sankerspace/Blumentopf/SensorNode/SensorNode.ino

/*
   Project: NESE_Blumentopf
   File:    SensorNode.ino
   Authors: Bernhard Fritz  (0828317@student.tuwien.ac.at)
            Marko Stanisic  (0325230@student.tuwien.ac.at)
            Helmut Bergmann (0325535@student.tuwien.ac.at)
   The copyright for the software is by the mentioned authors.

   This program uses a set of sensors to gather information about it's surrounding.
   It registers to a controller and periodically sends the data to the controller.
   During the measurements the setup goes into a low power mode.

*/


 

#include <JeeLib.h>   // For sleeping
//#include <dht11.h>    // Termperature and humidity sensork //!!!!!!!!!!!!!!!!!!!!!!!!!!!!!!!!!!!
#include <DHT.h>
#include <SPI.h>
//#include "nRF24L01.h" // radio
#include "RF24.h"     // radio
#include <EEPROM.h>

// For RTC:
#include <Time.h>
#include <TimeLib.h>


#include "Blumentopf.h"

//Marko@: One datastructure for both
//easier for Data Logging
struct Data myData;
struct Data myResponse;
class nodeList myNodeList;

/*
  // Hardware configuration for RF
  //
  signal  Arduino-Pin
* ** RF **
  CE      9
  CSN     10
  SCK     13
  MOSI    11
  MISO    12

* ** Sensors **
  VCC         8
  Brightness  A1
  Moisture    A0
  Temp&Hum    5
*/

// Set up nRF24L01 radio on SPI bus plus pins 9 & 10

RF24 radio(CE_PIN, CS_PIN);
DataStorage myEEPROM;

// Init the DS1302
// Set pins:  CE, IO,CLK

//RTC_DS1302 myRTC(2, 3, 4);    // change as needed. The Idea is that only the constructors need to be changed as another RTC is connected. So the RTC calls below should stay as they are.
#if (HW_RTC == RTC_1302)
RTC_DS1302 myRTC(2, 3, 4);  // CE, IO, CLK (RST, DAT, CLK)
#elif (HW_RTC == RTC_3231)
RTC_DS3231 myRTC;
#elif (HW_RTC == RTC_3232)
RTC_DS3232 myRTC;
#endif

// Setting the Sensor Pins
int moisturePin = MOISTURE_PIN;//A0
int moisturePin2 = MOISTURE_PIN_2;//A2
int lightPin = LIGHT_PIN;//A1
int sensorPower = SENSOR_POWER;//8

// Radio pipe addresses for the 2 nodes to communicate.
const uint64_t pipes[3] = {0xF0F0F0F0E1LL, 0xF0F0F0F0D2LL, 0xE8E8F0F0E1LL};



/*
    Hardware configuration for DHT11
*/


DHT dht(DHTPIN, DHTTYPE);



void setup_RF();
void printValues(int DHT_State);

ISR(WDT_vect)
{
  Sleepy::watchdogEvent();
}

// the setup function runs once when you press reset or power the board
void setup()
{

  int nRet;
  int nDelay;    // transmission duration in ms
  struct EEPROM_Data myEEPROMData;
  myData.state = 0;
  // initialize digital pin LED_BUILTIN as an output.
  pinMode(LED_BUILTIN, OUTPUT);
  pinMode(moisturePin, INPUT);
  pinMode(moisturePin2, INPUT);
  pinMode(lightPin, INPUT);
  pinMode(sensorPower, OUTPUT);
  pinMode(BATTERY_SENSE_PIN, INPUT);

  myResponse.interval = 100;  // at default repeat measurement every 2 seconds
//  killID();
  //  digitalWrite(sensorPower, LOW);   // turn off the sensor power
  digitalWrite(sensorPower, HIGH);   // turn off the sensor power
  delay(100);
  delay(400);     // RTC needs 500ms startup time in total

  setup_RF();       // initialize the RF24L01+ module

  // In  mode, output some stuff
#if DEBUG_
  Serial.begin(BAUD);
#endif




  DEBUG_PRINTSTR("SensorNode 1.0, ");
  DEBUG_PRINTLNSTR("----------------");

  //myEEPROM.unsetHeaders();
  myEEPROM.init();

  //    myEEPROM.delIndex();

  if (sizeof(struct Data) > 32)
  {
    DEBUG_PRINTLNSTR("Fatal error - too much sensor data. Restructure message protocol\n");
  }

  // setup the RTC
  //  setupRTC();
#if (HW_RTC > NONE)
#if (HW_RTC == RTC_1302)
  myRTC.init(&myData.state);
#elif (HW_RTC == RTC_3231)
  myRTC.init(&myData.state);
#elif (HW_RTC == RTC_3232)
  pinMode(HW_RTC_PIN, OUTPUT);
  digitalWrite(HW_RTC_PIN, HIGH);
  //Bernhard@: anschauen ob myrepsonse.state oder mydata.state
  //displayTime(RTC.get());
  myRTC.init(&(myResponse.state));
  //  displayTime(myRTC.getTime());
#endif
  displayTimeFromUNIX(myRTC.getTime());   // if there is a RTC --> display the time independently of the RTC type
#endif
  //  myResponse.ControllerTime = 1481803260;   // dummy time for testing..since I have only one RTC for testing
  //  myRTC.setTime(1486049640);

  myData.Time = myRTC.getTime();
  DEBUG_PRINTSTR("Time: ");
  displayTimeFromUNIX(myData.Time);

  // read EEPROM
  EEPROM.get(EEPROM_ID_ADDRESS, myEEPROMData);  // reading a struct, so it is flexible...
  myData.ID = myEEPROMData.ID;                  // passing the ID to the RF24 message

  //Marko@
  setDATA_SensorPacket(&myData);
  setDATA_NormalDatapacket(&myData); //from SensorNode to Controller
  setDATA_RegistrationPacket(&myData);

  //Marko@  The controller must be online before ANY Registration can be performed, otherwise undefined states // remark 2.6.2017: that shouldn't be the case!
  nRet = registerNode(&nDelay);
  while (nRet > 0)      // if the registration was not successful, retry until it is. Sleep inbetween
  {
    digitalWrite(sensorPower, LOW);   // turn off the sensor power
//    hibernate(myResponse.interval);
    hibernate(100 * (analogRead(randomPIN) % 60));  // sleep a random duration (< 60s) to avoid collisions
    //    Sleepy::loseSomeTime(myResponse.interval*100);
    digitalWrite(sensorPower, HIGH);   // turn on the sensor power
    delay(500);     // RTC needs 500ms startup time in total
    nRet = registerNode(&nDelay);
  }
  DEBUG_PRINTLNSTR("Initializing DHT Sensor.........");
  //Initialize DHT Sensor
  dht.begin();
  //  myRTC.adjustRTC(nDelay, &myData.state, myResponse.ControllerTime);

  //Marko@
  setDATA_NO_RegistrationPacket(&myData);
  DEBUG_PRINTSTR("[SENSORNODE]");
  DEBUG_PRINTSTR("[MYDATA PACKETINFO]:");
  DEBUG_PRINTDIG(myData.packetInfo, BIN);
  DEBUG_PRINTLNSTR("SETUP END SETUP END SETUP END SETUP END SETUP END SETUP END SETUP END SETUP END ");
  
#ifdef DEBUG_
  Serial.flush();
#endif
}



int registerNode(int *pnDelay)
{
  struct EEPROM_Data myEEPROMData;

  int nRet;

  //  if (myData.ID > 0)                        // this is a known node - 20170110...I guess this was the case on an old arduino. a new one showed 0xff in the EEPROM...
  if (myData.ID < 0xffff)                        // this is a known node - 20170110... this is the new check..
  {
    DEBUG_PRINTSTR("EEPROM-ID found: ");
    DEBUG_PRINT(myData.ID);                // Persistent ID
    DEBUG_PRINTLNSTR(". Registering at the server with this persistent ID... ");

    myData.state &= ~(1 << NEW_NODE_BIT);    // this is a known node
  }
  else                                      // this is a new node
  {
    DEBUG_PRINTSTR("No EEPROM-ID found. Registering at server with this random session ID: ");
    myData.state |= (1 << NEW_NODE_BIT);    // this is a new node

    // worked well as a random pattern generator, has some problems now:
    myData.temperature = (analogRead(randomPIN) % 100);

    DEBUG_PRINT(myData.temperature);
    DEBUG_PRINTLNSTR("...");

    // it is important to delete all previously collected data from the EEPROM, as the controller will not recognize the ID anymore.
    myEEPROM.stashData();

  }

  myData.state &= ~(1 << MSG_TYPE_BIT);     // set message type to init



  myData.humidity = 0;
  myData.moisture = 0;
  myData.moisture2 = 0;
  myData.brightness = 0;
  myData.voltage = 0;



  // send the request:
  nRet = RF_action(pnDelay);

  if (nRet == 0)          // There was a response
  {

    if (myData.state & (1 << NEW_NODE_BIT))       // This is a new node!
    {
      DEBUG_PRINTSTR("\tReceived Session ID: ");
      DEBUG_PRINT((int)(myResponse.interval / 100));

      DEBUG_PRINTSTR(",  expected: ");
      DEBUG_PRINT(myData.temperature);


      if (((int)(myResponse.interval / 100)) == (int) (myData.temperature))    // is the response for us? (yes, we stored the session ID in the temperature to keep the message small and reception easy...it could be changed to a struct in a "struct payload" which can be casted in the receiver depending on the status flags)
      {
        myData.ID = myResponse.ID;
        myData.interval = (myResponse.interval % 100);
        myEEPROMData.ID = myResponse.ID;
        EEPROM.put(EEPROM_ID_ADDRESS, myEEPROMData);   // writing the data (ID) back to EEPROM...

        DEBUG_PRINTLNSTR("...ID matches");
        DEBUG_PRINTSTR("\tPersistent ID: ");
        DEBUG_PRINT(myResponse.ID);
        DEBUG_PRINTSTR(", Interval: ");
        DEBUG_PRINTLN(myData.interval);
        DEBUG_PRINTLNSTR("\tStored Persistent ID in EEPROM...");
      }
      else                                                  // not our response
      {
        DEBUG_PRINTLNSTR("...ID missmatch! Ignore response...");
        return 11;
      }


    }
    else                                              // this is a known node
    {
      if (myResponse.ID == myData.ID)                     // is the response for us?
      {
        myData.interval = myResponse.interval;

        DEBUG_PRINTSTR("Got response for ID: ");
        DEBUG_PRINT(myResponse.ID);
        DEBUG_PRINTSTR("...ID matches, registration successful! Interval: ");
        DEBUG_PRINTLN(myData.interval);
      }
      else                                                  // not our response
      {
        DEBUG_PRINTSTR("Got response for ID: ");
        DEBUG_PRINT(myResponse.ID);
        DEBUG_PRINTLNSTR("...ID missmatch! Ignore response...");
        return 12;
      }
    }

  }
  else      // there was no response
  {
    // per default wait the same interval as before
    return nRet;
  }



  myData.state |= (1 << MSG_TYPE_BIT);    // set message to data

  return 0;   // all okay
}



// the loop function runs over and over again forever
void loop()
{
  int nDHT_Status;

  digitalWrite(LED_BUILTIN, HIGH);   // turn the LED on to indicate action

  digitalWrite(sensorPower, HIGH);   // turn on the sensor power and wait some time to stabilize
  delay(10);
  // initialises the RTC to save power
  DEBUG_PRINTLNSTR("\nPreparing a data message:");
  myRTC.init(&myData.state);



  delay(2000);    // DHT needs 1s to settle

  //Initialize DHT Sensor
  dht.begin();
  // The accuracy of the ADCs should be improved as in https://www.youtube.com/watch?v=E8GqHvOK4DI&feature=youtu.be
  // read the input on analog pin 0 (moisture):
  myData.moisture = analogRead(moisturePin);
  myData.moisture2 = analogRead(moisturePin2);

  // read the input on analog pin 1 (light):
  myData.brightness = analogRead(lightPin);



  myData.temperature  = dht.readTemperature();
  myData.humidity = dht.readHumidity();
  nDHT_Status = isnan((myData.temperature) || isnan( myData.humidity));
  // getting the battery state:
  myData.voltage = getBatteryVoltage();   // sollten wir diese Methode verwenden, muss sie adaptiert werden. Sie verändert die ADC-Einstellungen


#if DEBUG_
  printValues(nDHT_Status);
  printFreeRam();
#endif

  myData.state &= ~(1 << EEPROM_DATA_PACKED); // this is live data


  // reads the current real time value
  myData.Time = myRTC.getTime();
  DEBUG_PRINTSTR("\tTime: ");
  displayTimeFromUNIX(myData.Time);
  digitalWrite(sensorPower, LOW);   // when we finished measuring, turn the sensor power off again



  myData.ID = getMyID();        // 20170607 - in case wrong EEPROM data is read (what shouldn't happen of course, but might), the ID is overwritten. So make sure to always transmit the correct ID!
  sendData();



  delay(PRE_SLEEP_DELAY);                       // finish the serial communication and RF communication
  digitalWrite(LED_BUILTIN, LOW);    // turn the LED off for sleeping
#ifdef DEBUG_
  Serial.flush();
#endif

  turnOffOutputs();
  //  Sleepy::loseSomeTime(myResponse.interval * 100);
  //  Sleepy::loseSomeTime(nSleepInterval * 1000);
  hibernate(myNodeList.mnCurrentInterval * 10);
  //delay(myResponse.interval * 100);

}

uint16_t getMyID()
{
  struct EEPROM_Data myEEPROMData;
  
  EEPROM.get(EEPROM_ID_ADDRESS, myEEPROMData);  // reading a struct, so it is flexible...
  return myEEPROMData.ID;                  // passing the ID to the RF24 message
}
  
/*
   If the RTC pins are not turned off, they will consume 170µA during sleep
*/

void turnOffOutputs()
{
  //  digitalWrite(A4, LOW);
  pinMode(A4, INPUT);
  //  digitalWrite(A5, LOW);
  pinMode(A5, INPUT);
}

void sendData()
{
  bool sending = true;
  int nRet;
  int nDelay;
  myData.state |= (1 << MSG_TYPE_BIT);    // set message to data
  myData.state &= ~(1 << NODE_TYPE);      // set node type to sensor
  while (sending == true)
  {
    //    DEBUG_PRINT("-");
    //    DEBUG_PRINTLN(myData.state);
    nRet = RF_action(&nDelay);

    if (nRet == 0)  // got a response
    {
      /*      Serial.print(":");
            Serial.println(myResponse.state);
            Serial.print(" / ResponseID: ");
            Serial.println(myResponse.ID);
            Serial.print(" / myID: ");
            Serial.println(myData.ID);
      */
      if (myResponse.ID == myData.ID)     // response is for us
      {
        if ((myData.state & (1 << EEPROM_DATA_PACKED)) == false)     // transmitted live data
        {
          DEBUG_PRINTSTR("\tResponse is valid, next measurement in ");
          //          DEBUG_PRINT(myResponse.interval / 10);
          DEBUG_PRINT(myResponse.interval);
          //          myResponse.interval = 100;
          myNodeList.mnCurrentInterval = myResponse.interval;      // this is the actual time to sleep...
          DEBUG_PRINTLNSTR(" seconds.");
          digitalWrite(sensorPower, HIGH);   // when we finished measuring, turn the sensor power off again
          delay(10);
          myRTC.adjustRTC(nDelay, &myData.state, myResponse.Time);//ControllerTime
          delay(10);
          digitalWrite(sensorPower, LOW);   // when we finished measuring, turn the sensor power off again
        }
        // in case EEPROM data has been transmitted, we skip the clock synchronisation. The synchronisation has been checked some milliseconds ago.
        // However the transmitted data element has to be removed from the EEPROM
        else
        {
          freeEEPROMdata();         // remove data from the memory
        }
        if (EEPROM_data_available() == true)
        {
          DEBUG_PRINTLNSTR("\tData available in EEPROM");

          switch (myResponse.state &  FETCH_EEPROM_REG_MASK)
          {
            case FETCH_EEPROM_REG_SKIP :     // controller doesn't want EEPROM data..go to sleep
              DEBUG_PRINTLNSTR("\tThe controller doesn't want EEPROM data now.");
              sending = false;
              break;
            case FETCH_EEPROM_REG_SEND :     // controller wants EEPROM data now
              DEBUG_PRINTLNSTR("\tThe controller wants the EEPROM data now");
              fetchEEPROMdata(&myData);           // get data for retransmission       // hsould only be called when there is data to transmit
              myData.state |= (1 << MSG_TYPE_BIT);    // set message to data
              sending = true;

              myData.state |= (1 << EEPROM_DATA_PACKED); // this is EEPROM data

              break;
            case FETCH_EEPROM_REG_DELETE :     // controller doesn't want EEPROM data..delete it
              DEBUG_PRINTLNSTR("\tThe controller wants the EEPROM data to be deleted");
              //              deleteEEPROM();
              myEEPROM.stashData();
              sending = false;
              break;
            default:  // shouldn't happen!!
              sending = false;
              break;
          }
        }
        else
        {
          DEBUG_PRINTLNSTR("\tNo data available in EEPROM");
          sending = false;
        }

      }
      else      // the response is for another node
      {
        DEBUG_PRINTLNSTR("\tResponse is for another node.");
        if ((myData.state & (1 << EEPROM_DATA_PACKED)) == false)     // transmitted live data
        {
          store_DATA_to_EEPROM();
          // The interval duration should be the same as before..
          DEBUG_PRINTSTR("\tNext measurement in ");
          DEBUG_PRINT(myNodeList.mnCurrentInterval);
          DEBUG_PRINTLNSTR(" seconds.");
        }
        sending = false;
        // otherwise we do not care..start sleeping
      }

      // Todo : Check whether data is stored in EEPROM and send it if requested

    }
    else            // no response or transmission failed. Store data in EEPROM and try again later.
    {
      if ((myData.state & (1 << EEPROM_DATA_PACKED)) == false)     // transmitted live data
      {
        store_DATA_to_EEPROM();
        // The interval duration should be the same as before..
        DEBUG_PRINTSTR("\tNext measurement in ");
        DEBUG_PRINT(myNodeList.mnCurrentInterval);
        DEBUG_PRINTLNSTR(" seconds.");
      }
      // otherwise we do not care..start sleeping anyway
      sending = false;
    }
  }
}

/*
   Stores data which could not be sent to the EEPROM.
   The algorithm evenly uses the EEPROM storage.
   For example:
    Address examples for data information headers are: 100, 200, 300, 400, 500, 600, 700, 800, 900, 1000
    The headers are browsed, always just one header is valid. After the EEPROM data is requested from the controller, the next header is used.
    The block addess of the actual data is stored in the header element.
*/
void store_DATA_to_EEPROM()
{
  myEEPROM.add(myData);
  myEEPROM.printElements();
}


/*
   Get last EEPROM data item
   In case of non-overflow this is  the item at the end of the chain.
   In the overflow-situation this means the oldest item will be retrieved.
*/
void fetchEEPROMdata(struct Data* nextData)//sensorData
{
  DEBUG_PRINTLNSTR("\t\tGetting a data element for transmission..");
  //  struct sensorData nextData;
  myEEPROM.readNextItem(nextData);
  //  DEBUG_PRINTLNSTR("done");
}

/*
   Get last EEPROM data item
   In case of non-overflow this is  the item at the end of the chain.
   In the overflow-situation this means the oldest item will be retrieved.
*/
void freeEEPROMdata()
{
  DEBUG_PRINTLNSTR("\tDeleting the transmitted data element from EEPROM..");
  myEEPROM.freeNextItem();
  DEBUG_PRINTLNSTR("done");
}

/*
   setup_RF initializes the RF24L01+ for the application.
*/

//void setup_RF(RF24* radio)
void setup_RF()
{

  //
  // Setup and configure rf radio
  //

  //radio.begin();
  radio.begin(RADIO_AUTO_ACK, RADIO_DELAY, RADIO_RETRIES, RADIO_SPEED, RADIO_CRC, RADIO_CHANNEL, RADIO_PA_LEVEL);
  // optionally, increase the delay between retries & # of retries
  // radio.setRetries(15,15);

  // optionally, reduce the payload size. seems to
  // improve reliability
  //  radio.setPayloadSize(4);

  // transmission settings:
  //  radio.setPALevel(RF24_PA_MIN);

  //radio.setChannel(RADIO_CHANNEL);  // Above most Wifi Channels

  //
  // Open pipes to other nodes for communication
  //

  // This simple sketch opens two pipes for these two nodes to communicate
  // back and forth.
  // Open 'our' pipe for writing
  // Open the 'other' pipe for reading, in position #1 (we can have up to 5 pipes open for reading)


  radio.openWritingPipe(pipes[1]);
  radio.openReadingPipe(1, pipes[0]);

  //
  // Start listening
  //

  // radio.startListening();

  //
  // Dump the configuration of the rf unit for debugging
  //

  radio.printDetails();

}



uint16_t averageADC(uint8_t ADCpin, uint8_t cycles)
{
  uint8_t i;
  uint32_t nValue = 0;
  for (i = 0; i < 8; i++)  // burn some readings
  {
    analogRead(ADCpin);
  }

  for (i = 0; i < cycles; i++)
  {
    nValue += analogRead(ADCpin);
  }

  return (nValue / cycles);
}


uint16_t getBatteryVoltage()
{

  analogReference(INTERNAL); //set the ADC reference to 1.1V
  burn8Readings(BATTERY_SENSE_PIN); //make 8 readings but don't use them to ensure good reading after ADC reference change
  delay(20);
  //  uint16_t nResult = analogRead(BATTERY_SENSE_PIN);
  uint16_t nResult = averageADC(BATTERY_SENSE_PIN, 5);


  analogReference(DEFAULT); //set the ADC reference back to internal
  burn8Readings(BATTERY_SENSE_PIN); //make 8 readings but don't use them to ensure good reading after ADC reference change
  delay(20);


  /*  DEBUG_PRINTSTR("\n nResult: ");
    DEBUG_PRINTLN(nResult);
    DEBUG_PRINTDIG(V_ADC_max, 2);
    DEBUG_PRINTLNSTR("");
  */

  float fVoltage = 100.0 * nResult * VOLTAGE_DIVIDER_FACTOR * V_ADC_max / (1024);


  return (uint16_t) fVoltage;
}

// From https://github.com/ForceTronics/nRF24L01_Wireless_Sensor_Dev_Board/blob/master/WSNode.cpp :
//This function uses the known internal reference value of the 328p (~1.1V) to calculate the VCC value which comes from a battery
//This was leveraged from a great tutorial found at https://code.google.com/p/tinkerit/wiki/SecretVoltmeter?pageId=110412607001051797704
uint16_t getVCCVoltage()
{
  analogReference(EXTERNAL); //set the ADC reference to AVCC
  burn8Readings(A0); //make 8 readings but don't use them to ensure good reading after ADC reference change
  int buffer = ADMUX;
  ADMUX = _BV(REFS0) | _BV(MUX3) | _BV(MUX2) | _BV(MUX1);
  unsigned long start = millis(); //get timer value
  while ( (start + 3) > millis()); //delay for 3 milliseconds
  ADCSRA |= _BV(ADSC); // Start ADC conversion
  while (bit_is_set(ADCSRA, ADSC)); //wait until conversion is complete
  int result = ADCL; //get first half of result
  result |= ADCH << 8; //get rest of the result
  uint16_t batVolt = (IREF / result) * 102400; //Use the known iRef to calculate battery voltage [in 0.01V]
  ADMUX = buffer;
  analogReference(DEFAULT); //set the ADC reference back to internal
  burn8Readings(A0); //make 8 readings but don't use them to ensure good reading after ADC reference change
  //  burn8Readings(A1); //make 8 readings but don't use them to ensure good reading after ADC reference change
  return batVolt;
}



//This function makes 8 ADC measurements but does nothing with them
//Since after a reference change the ADC can return bad readings. This function is used to get rid of the first
//8 readings to ensure next reading is accurate
void burn8Readings(int pin)
{
  for (int i = 0; i < 8; i++) {
    analogRead(pin);
  }
}

void printValues(int DHT_State)//!!!!!!!!!!!!!!!!!!!!!!!!!!!!!!!!!!!!!
{
  char cDegreeSymbol = 176;

  // Print the Temperature and Humidity values:
  if (DHT_State == 0)//!!!!!!!!!!!!!!!!!!!!!!!!!!!!!!!!!!!!!
  {
    DEBUG_PRINTSTR("\tHumidity:    ");
    DEBUG_PRINTDIG((float) myData.humidity , 2);
    DEBUG_PRINTLN("%");

    DEBUG_PRINTSTR("\tTemperature: ");
    DEBUG_PRINTDIG((float) myData.temperature , 2);
    DEBUG_PRINT(cDegreeSymbol);
    DEBUG_PRINTLN("C");

  }
  else
  {
    DEBUG_PRINTLNSTR("\t[ERROR] Failed to read from DHT sensor!");
  }


  // Print the light value
  if (myData.brightness < LIGHT_THRESHOLD)
  {
    DEBUG_PRINTSTR("\tIt is night (");
    DEBUG_PRINT(myData.brightness);
    DEBUG_PRINTLN(")");
  }
  else
  {
    DEBUG_PRINTSTR("\tIt is day   (");
    DEBUG_PRINT(myData.brightness);
    DEBUG_PRINTLN(")");
  }


  // Print the moisture value
  if (myData.moisture < MOISTURE_THRESHOLD)
  {
    DEBUG_PRINTSTR("\tThe plant1 doesn't need watering (");
    DEBUG_PRINT(myData.moisture);
    DEBUG_PRINTLN(")");
  }
  else {
    DEBUG_PRINTSTR("\tIt is time to water plant1   (");
    DEBUG_PRINT(myData.moisture);
    DEBUG_PRINTLN(")");
  }
  if (myData.moisture2 < MOISTURE_THRESHOLD)
  {
    DEBUG_PRINTSTR("\tThe plant2 doesn't need watering (");
    DEBUG_PRINT(myData.moisture2);
    DEBUG_PRINTLN(")");
  }
  else {
    DEBUG_PRINTSTR("\tIt is time to water plant2   (");
    DEBUG_PRINT(myData.moisture2);
    DEBUG_PRINTLN(")");
  }

  DEBUG_PRINTSTR("\tVoltage:     ");
  DEBUG_PRINT(myData.voltage);
  DEBUG_PRINTLN("V");
  return;
}

/*
   Checks whether there is unsent data waiting in the EEPROM
*/
bool EEPROM_data_available()
{
  //  return false;
  return !myEEPROM.getEmpty();
}


//void RF_action(RF24* radio)
int RF_action(int* pnDelay)
{

  // First, stop listening so we can talk.
  radio.stopListening();

  if (EEPROM_data_available() == true)      // there is EEPROM data
  {
    myData.state |= (1 << EEPROM_DATA_AVAILABLE);
  }
  else                                    // no EEPROM data
  {
    myData.state &= ~(1 << EEPROM_DATA_AVAILABLE);
  }


  //    myData.realTime = myRTC.getTime();  // darf hier nicht aufgerufen werden, weil RTC abgedreht ist.

  // Send the measurement results
  DEBUG_PRINTSTR("Sending data...");
  //    DEBUG_PRINT(myData.state);
  DEBUG_PRINTSTR("ID: ");
  DEBUG_PRINTLN(myData.ID);
  //myData.dummy16=0;//sensorData will be send //Marko@ habs mal auskommentiert , brauchtest du die variable?
  radio.write(&myData, sizeof(struct Data));

  delay(10);
  // Now, continue listening
  radio.startListening();



  // Wait here until we get a response, or timeout (250ms)
  unsigned long started_waiting_at = millis();
  bool timeout = false;
  while ( (radio.available() == 0 ) && ! timeout )
  {
    if (millis() - started_waiting_at > REGISTRATION_TIMEOUT_INTERVAL )
    {
      timeout = true;
    }
  }

  // Describe the results
  if ( timeout )
  {
    DEBUG_PRINTLNSTR("\tFailed, response timed out.");
    DEBUG_PRINTSTR("\t\tStarted to wait at: ");
    DEBUG_PRINT(started_waiting_at);
    DEBUG_PRINTSTR("\t\t current time: ");
    DEBUG_PRINTLN(millis());
    radio.powerDown();
    return 1;
  }
  else      // There was a response - read the new interval
  {
    // Grab the response, compare, and send to debugging spew
    unsigned long got_time;
    got_time = millis();
    radio.read( &myResponse, sizeof(struct Data) );

    // Show response:
    //printf("Got response %lu, round-trip delay: %lu\n\r",got_time,millis()-got_time);

    DEBUG_PRINTSTR("\tGot response (Round-trip delay: ");
    *pnDelay = millis() - started_waiting_at;
    DEBUG_PRINT(*pnDelay);
    DEBUG_PRINTLN(" ms)");


  }

  radio.powerDown();

  return 0;
}


/*
   This function sends the ATMega to sleep for a time given in [s/10].
   It is not totally accurate, so at some point it should use the RTC as adjustment.
*/
void hibernate(uint16_t duration)
{
  while (duration > 600)   // more than 60 seconds?
  {
    Sleepy::loseSomeTime(60000);  // sleep one minute
    duration -= 600;
  }
  Sleepy::loseSomeTime(duration * 100);
}




//TODO:

/*Check if that is resolved???

  (Readme.md)If RTC is unplugged, sketch will hang due to a bug in the I2C library.

*/
